swaziloo/halloween/animatronicCrow/images/AniCrow002.jpg

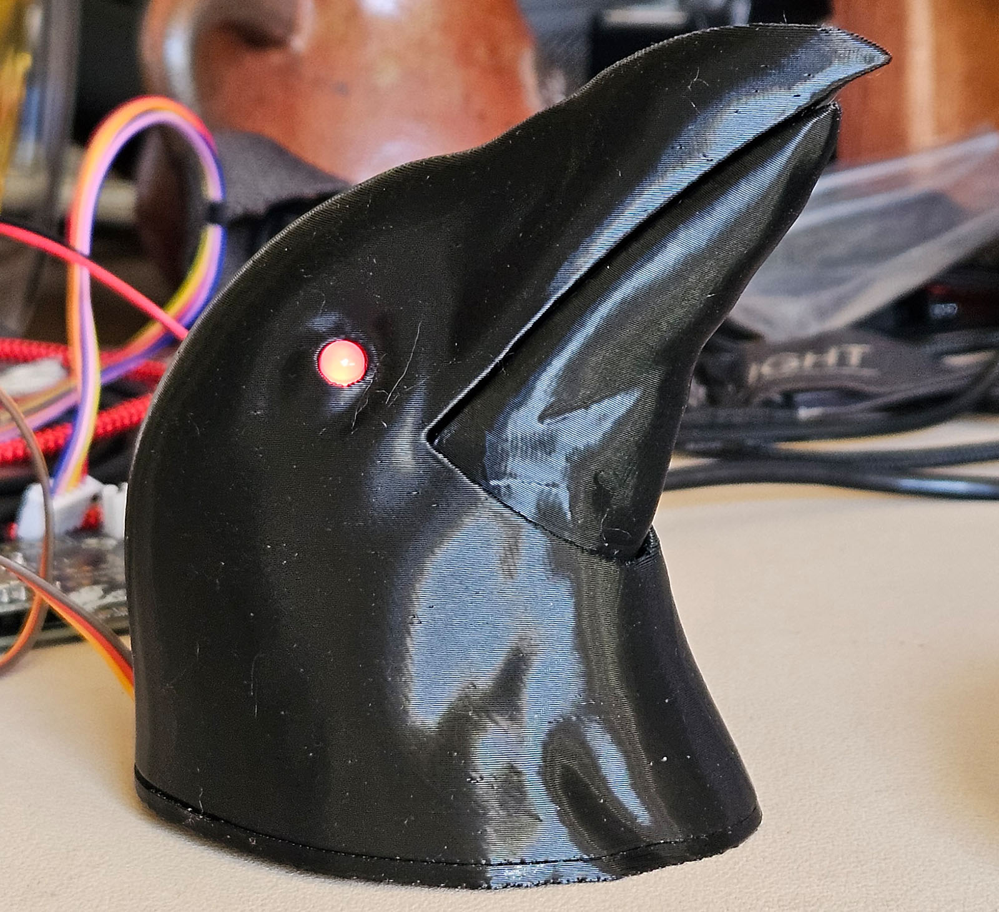
animatronicCrow/images/AniCrow002.jpg
