swaziloo/halloween/animatronicCrow/images/AniCrow003.jpg

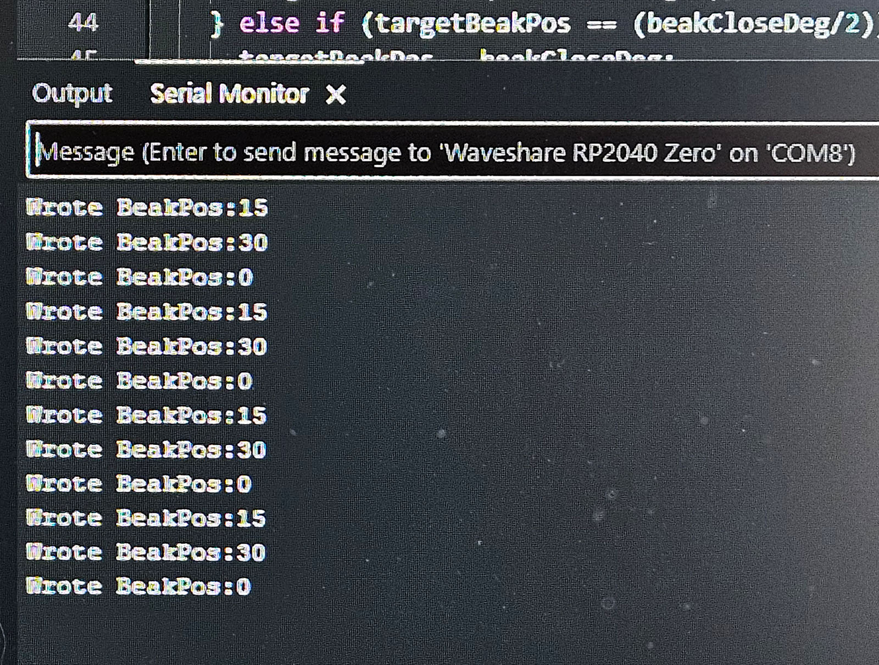
animatronicCrow/images/AniCrow003.jpg
