swaziloo/halloween/animatronicCrow/images/AniCrow004.jpg

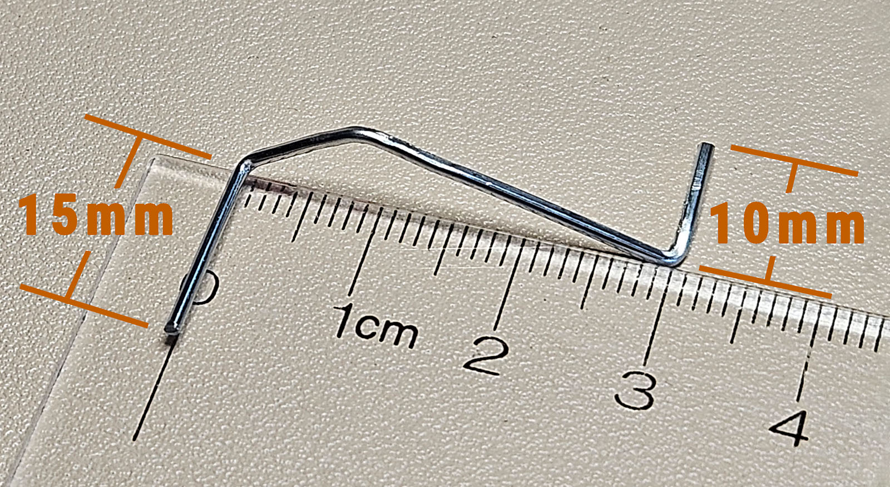
animatronicCrow/images/AniCrow004.jpg
