swaziloo/halloween/animatronicCrow/images/AniCrow005.jpg

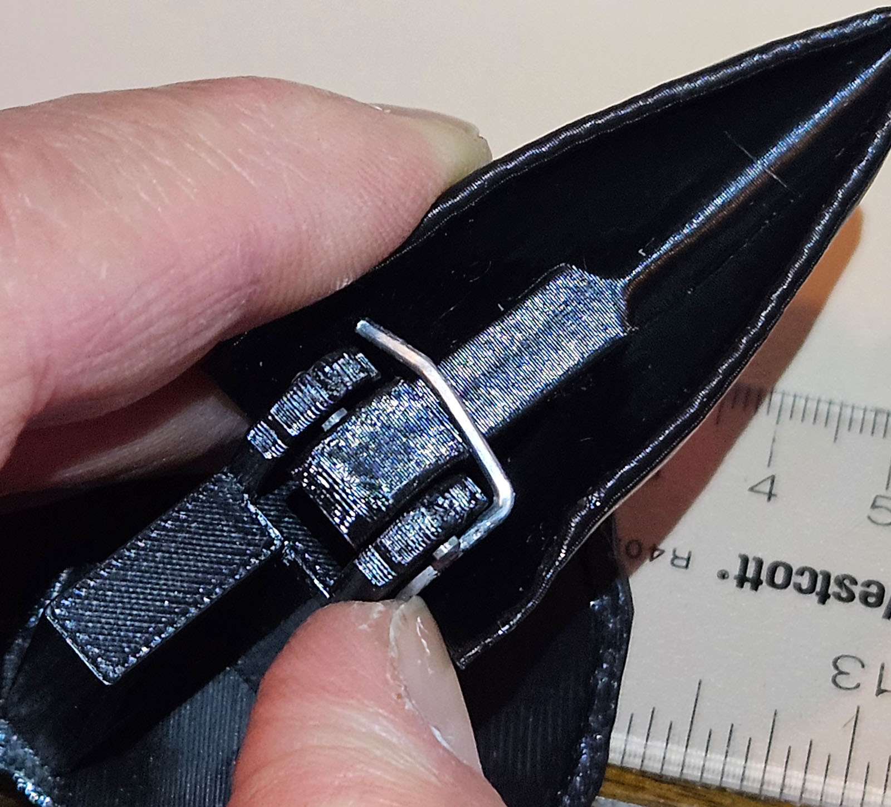
animatronicCrow/images/AniCrow005.jpg
