swaziloo/halloween/animatronicCrow/images/AniCrow006.jpg

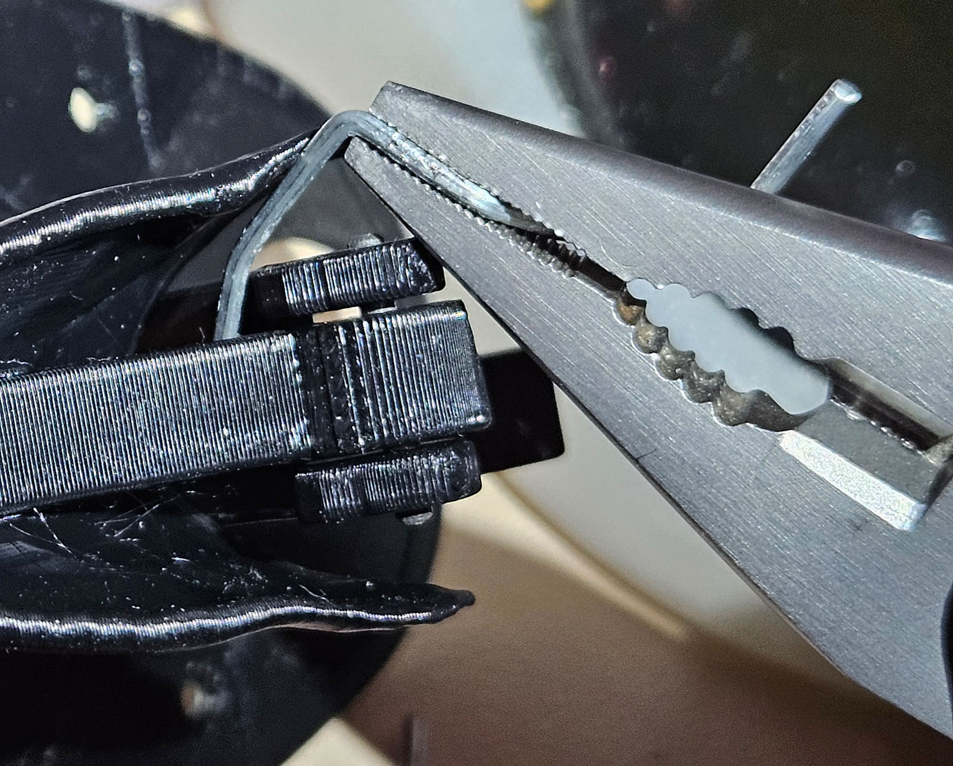
animatronicCrow/images/AniCrow006.jpg
