swaziloo/halloween/animatronicCrow/images/AniCrow007.jpg

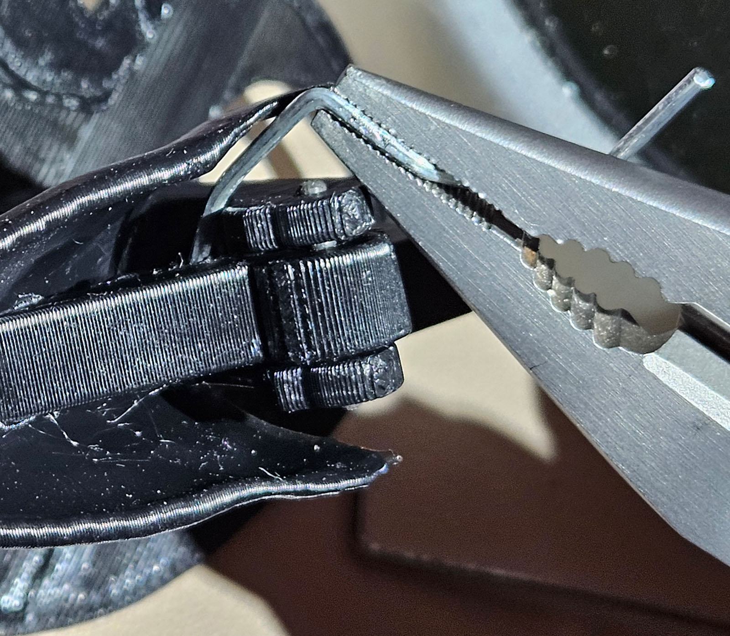
animatronicCrow/images/AniCrow007.jpg
