swaziloo/halloween/animatronicCrow/images/AniCrow008.jpg

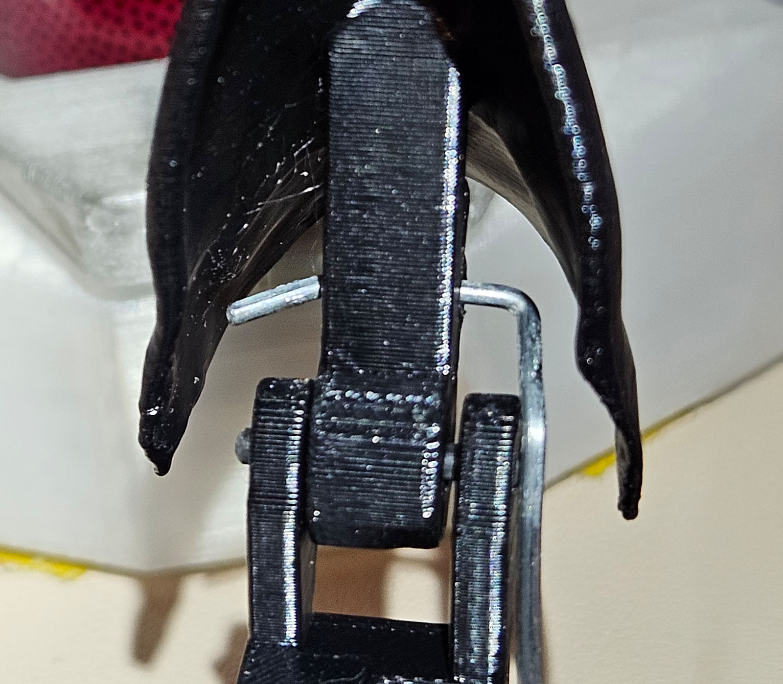
animatronicCrow/images/AniCrow008.jpg
