swaziloo/halloween/animatronicCrow/images/AniCrow009.jpg

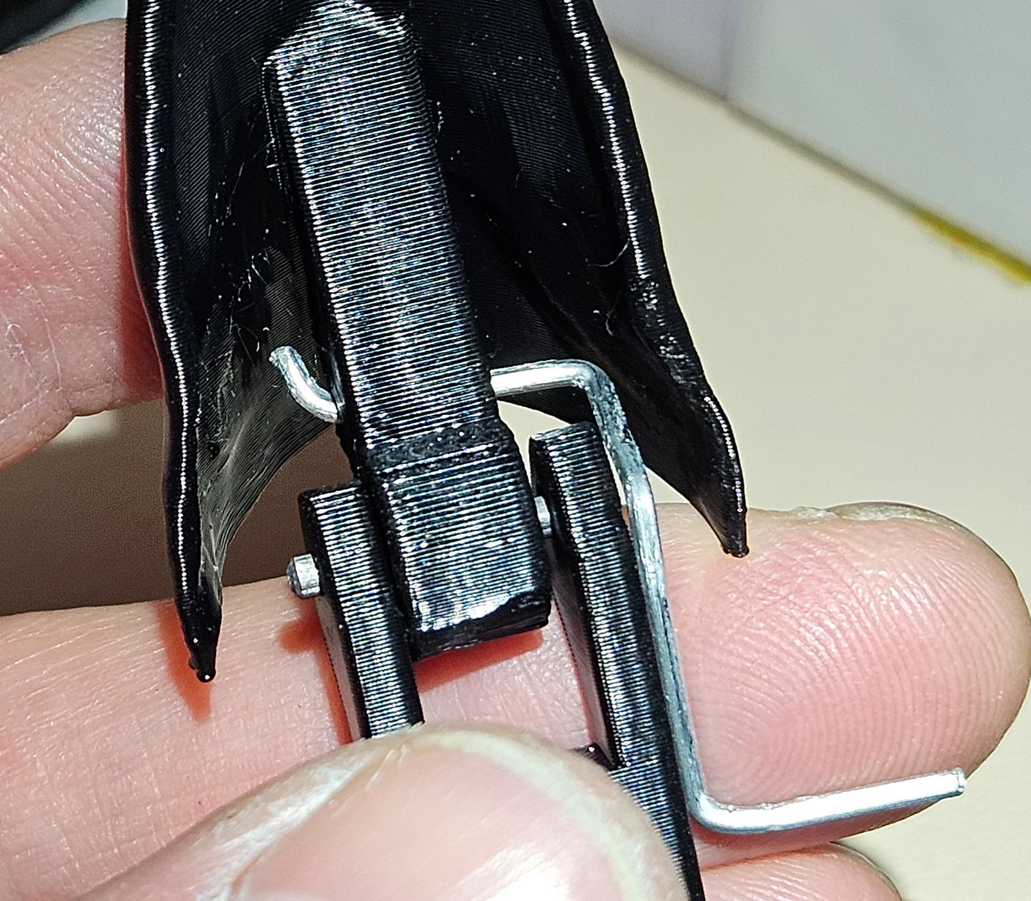
animatronicCrow/images/AniCrow009.jpg
