swaziloo/halloween/animatronicCrow/images/AniCrow019.jpg

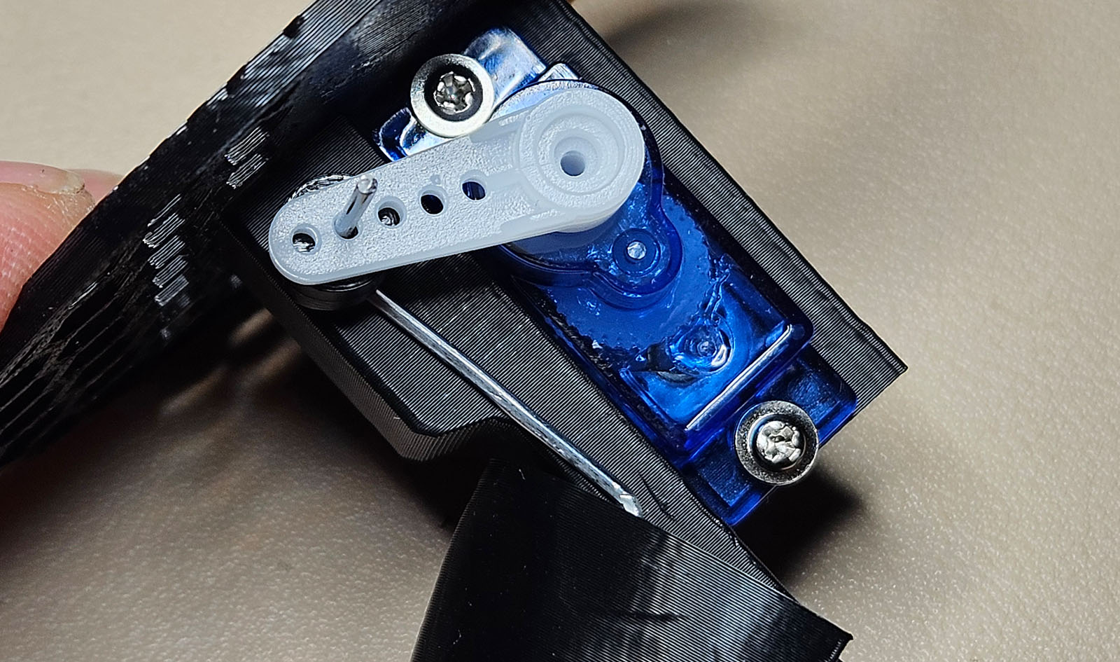
animatronicCrow/images/AniCrow019.jpg
