swaziloo/halloween/animatronicCrow/images/AniCrow020.png

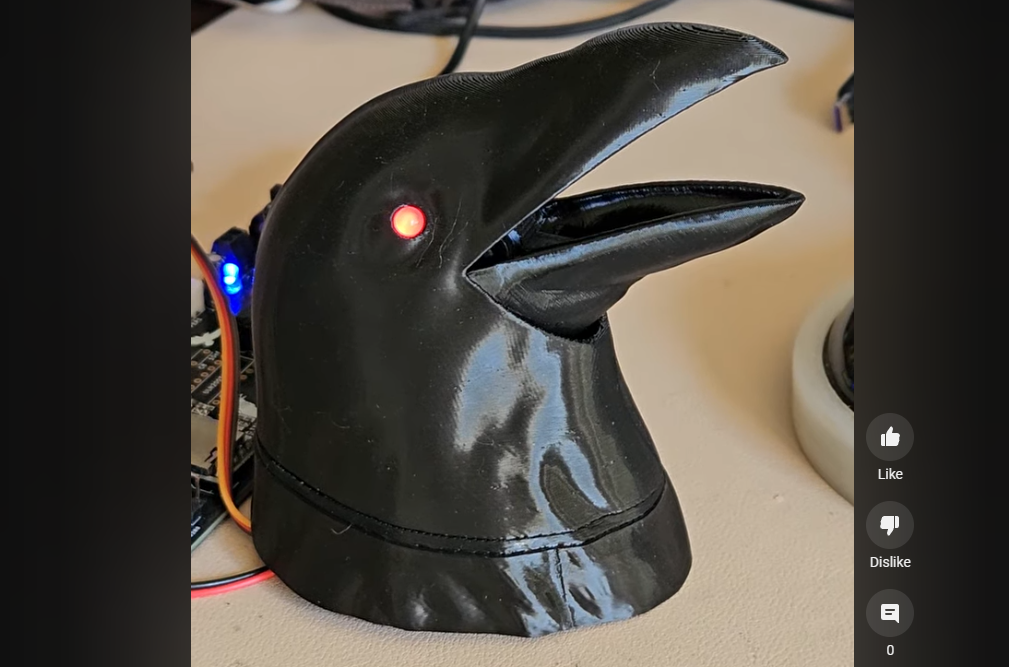
animatronicCrow/images/AniCrow020.png
