swaziloo/halloween/animatronicCrow/images/AniCrow021.png

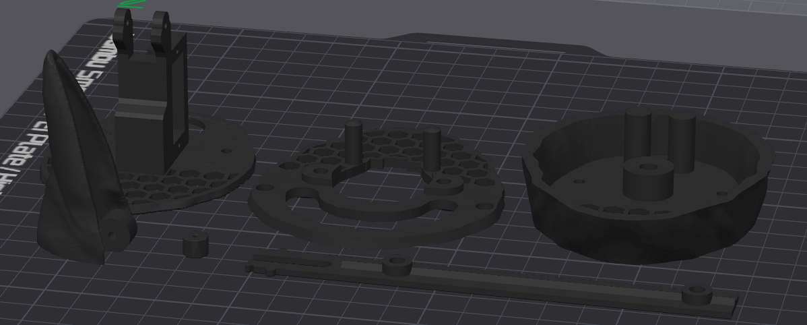
animatronicCrow/images/AniCrow021.png
