swaziloo/halloween/animatronicCrow/images/AniCrow023.jpg

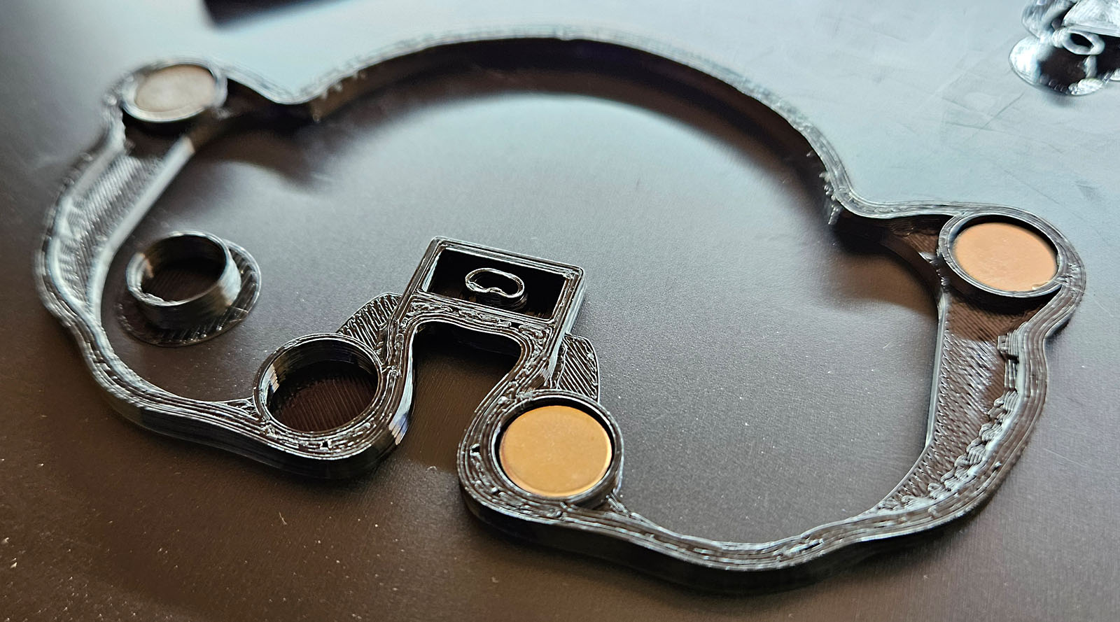
animatronicCrow/images/AniCrow023.jpg
