swaziloo/halloween/animatronicCrow/images/AniCrow025.jpg

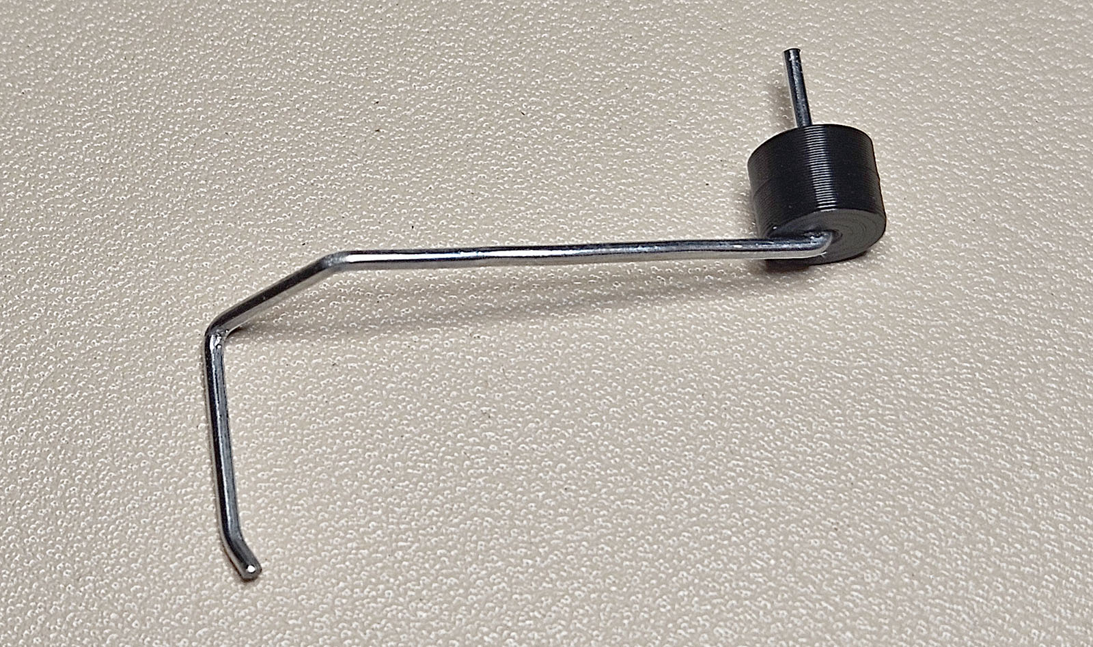
animatronicCrow/images/AniCrow025.jpg
