swaziloo/halloween/animatronicCrow/images/AniCrow026.png

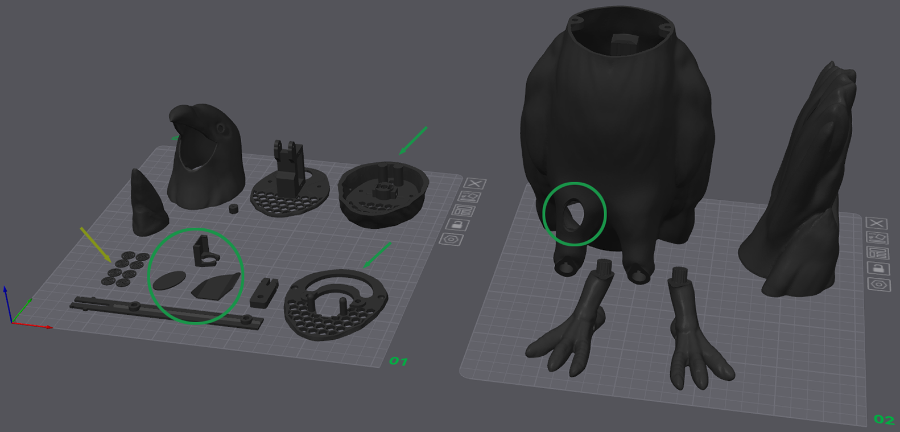
animatronicCrow/images/AniCrow026.png
