swaziloo/halloween/animatronicCrow/images/AniCrow027.png

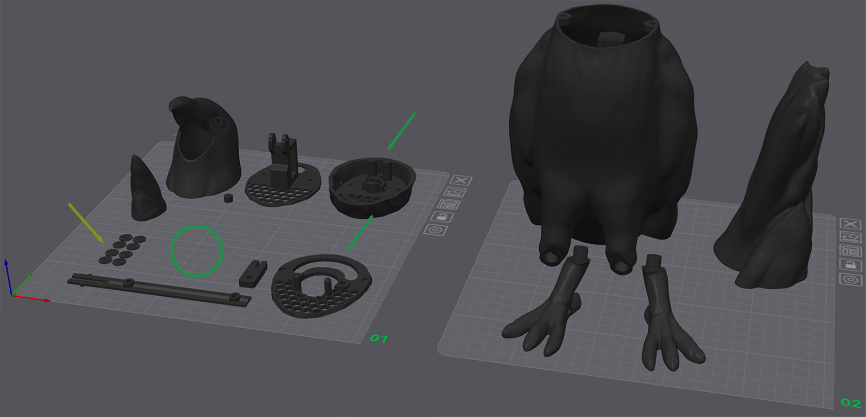
animatronicCrow/images/AniCrow027.png
