swaziloo/halloween/animatronicCrow/images/AniCrow028.jpg

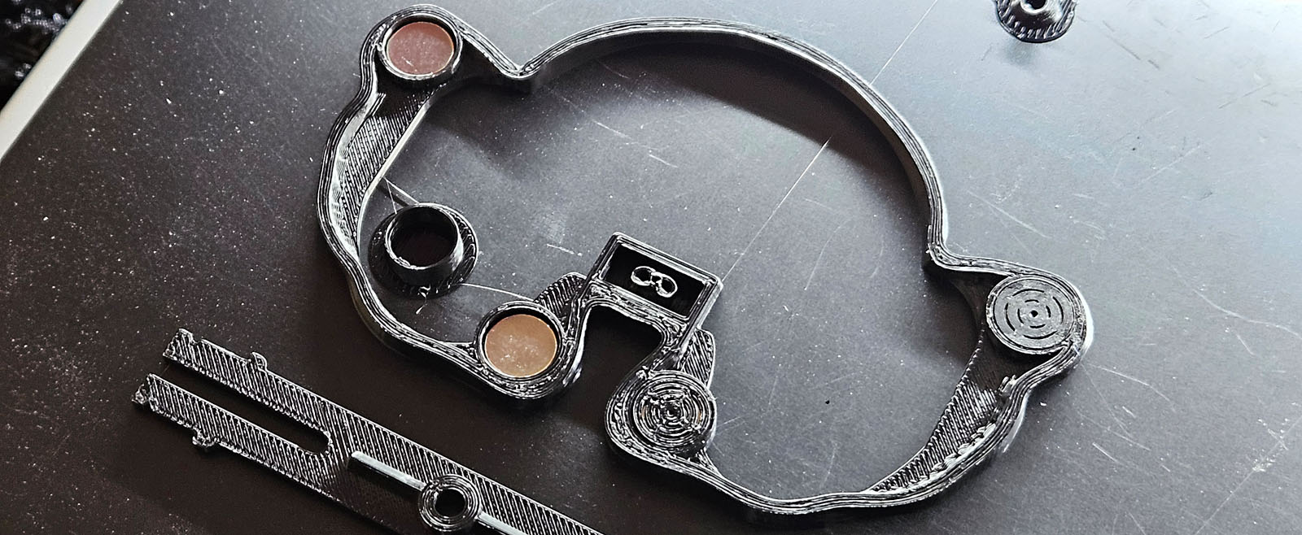
animatronicCrow/images/AniCrow028.jpg
