swaziloo/halloween/animatronicCrow/images/AniCrow035.jpg

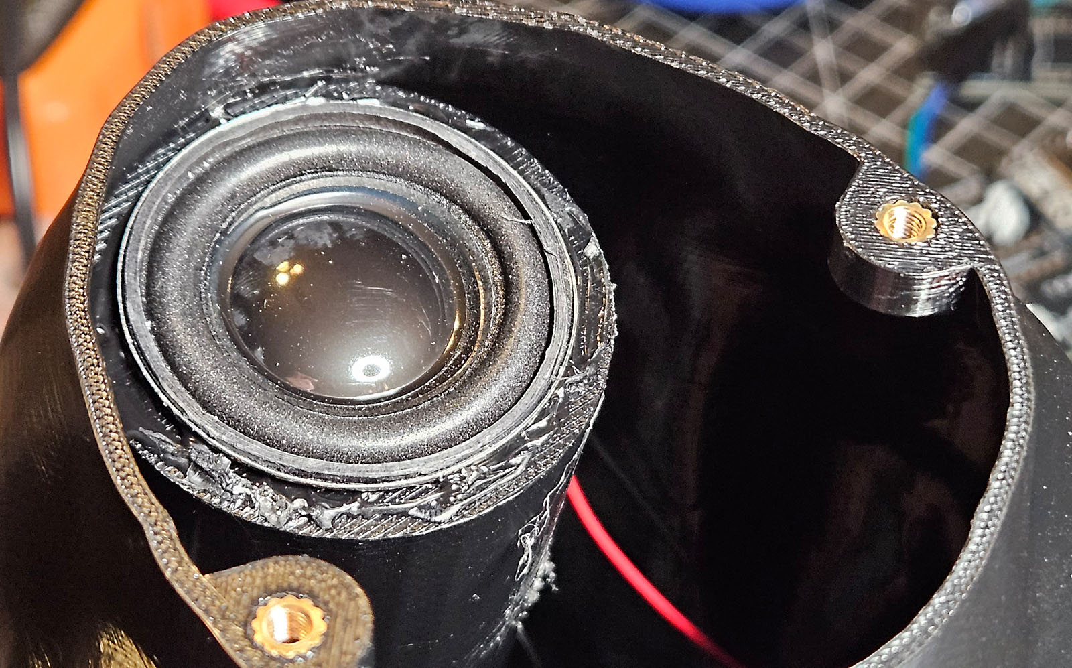
animatronicCrow/images/AniCrow035.jpg
