swaziloo/halloween/animatronicCrow/images/AniCrow037.jpg

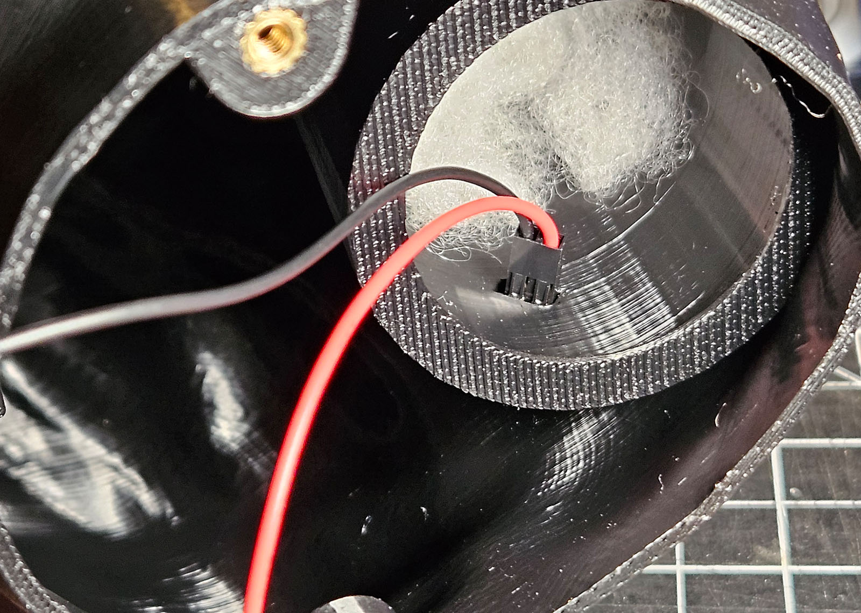
animatronicCrow/images/AniCrow037.jpg
