swaziloo/halloween/animatronicCrow/images/AniCrow041.jpg

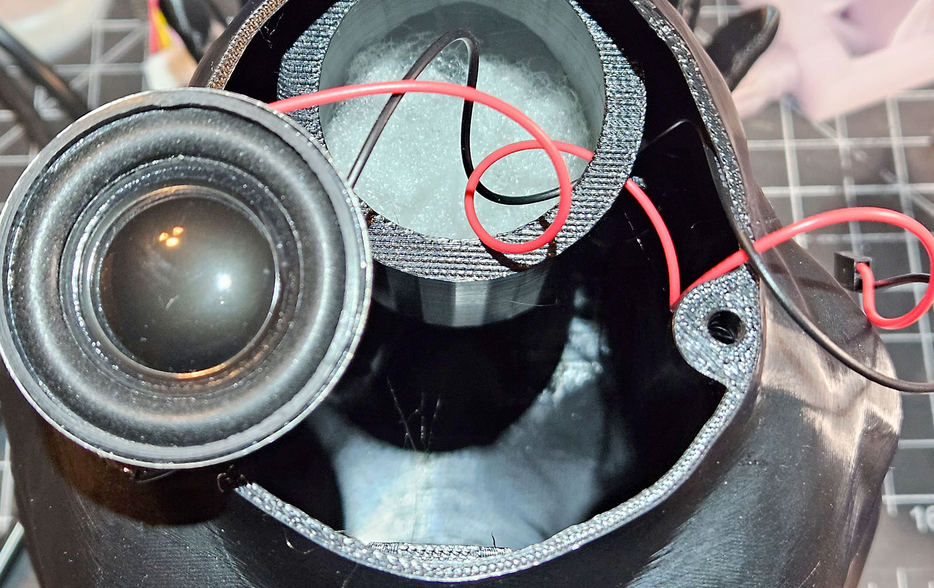
animatronicCrow/images/AniCrow041.jpg
