swaziloo/halloween/animatronicCrow/images/AniCrow042.jpg

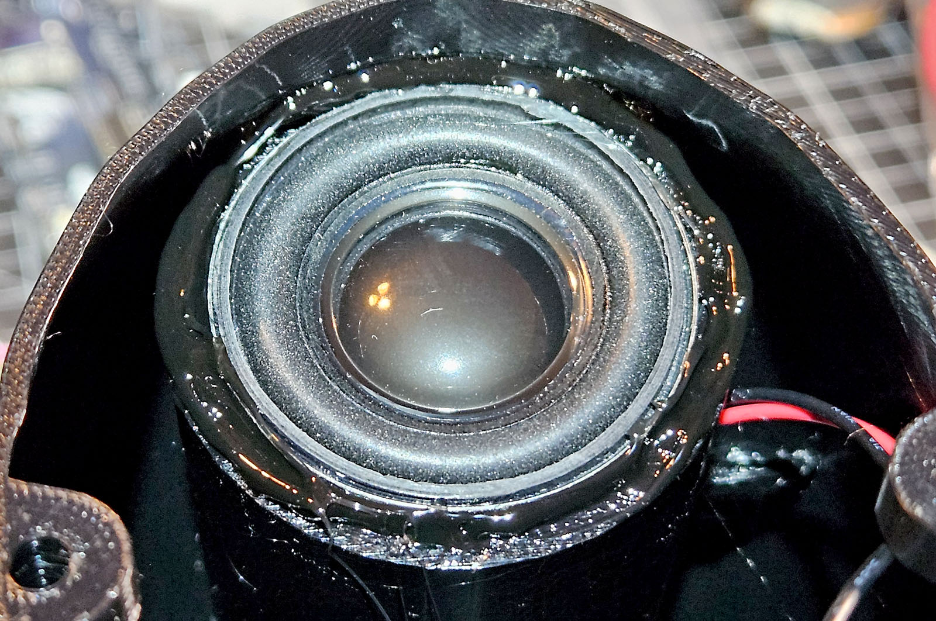
animatronicCrow/images/AniCrow042.jpg
