swaziloo/halloween/animatronicCrow/images/AniCrow043.jpg

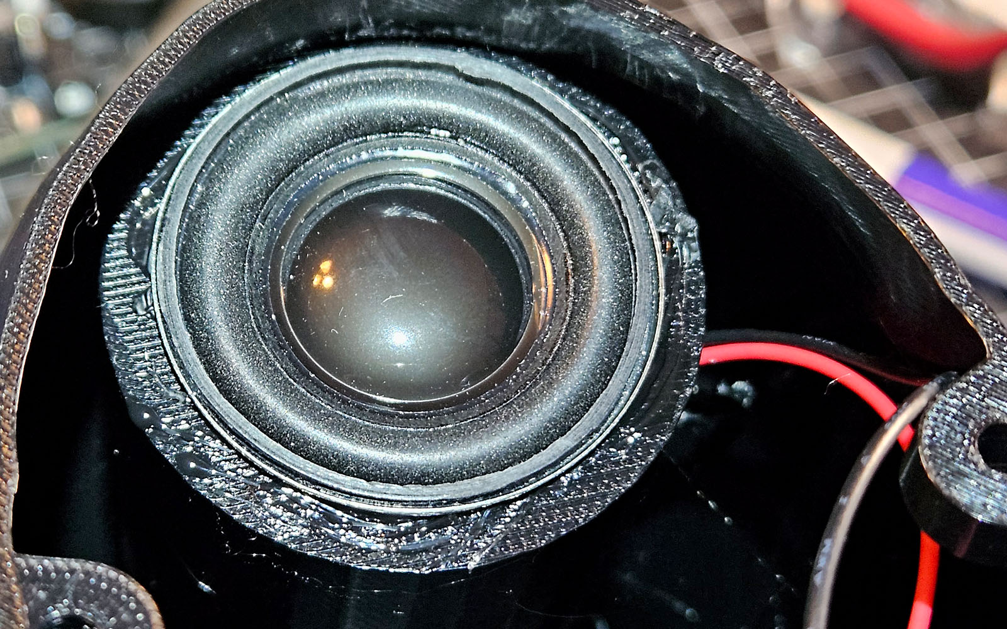
animatronicCrow/images/AniCrow043.jpg
