swaziloo/halloween/animatronicCrow/images/AniCrow044.jpg

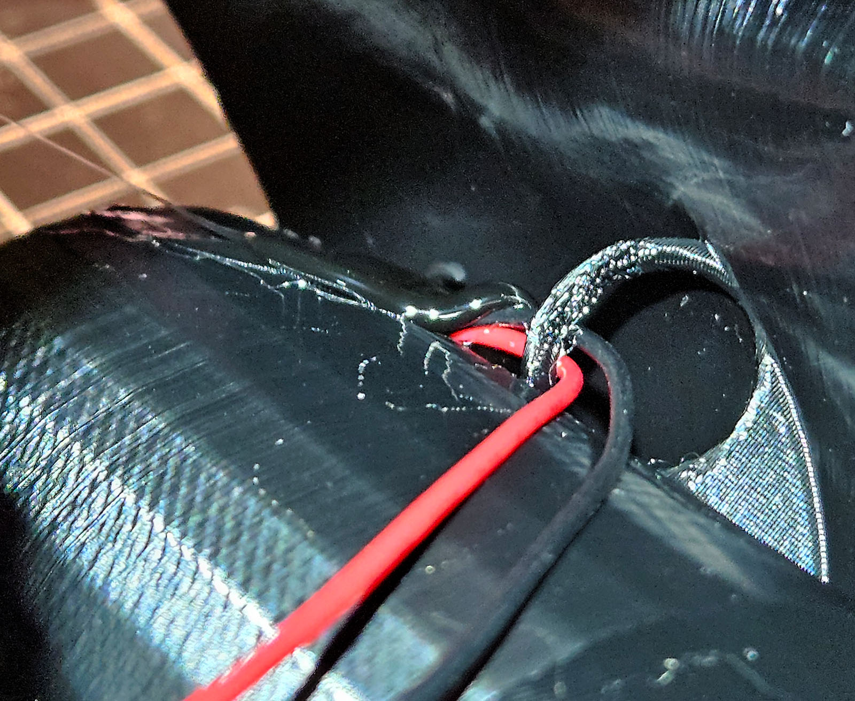
animatronicCrow/images/AniCrow044.jpg
