swaziloo/halloween/animatronicCrow/images/AniCrow047.jpg

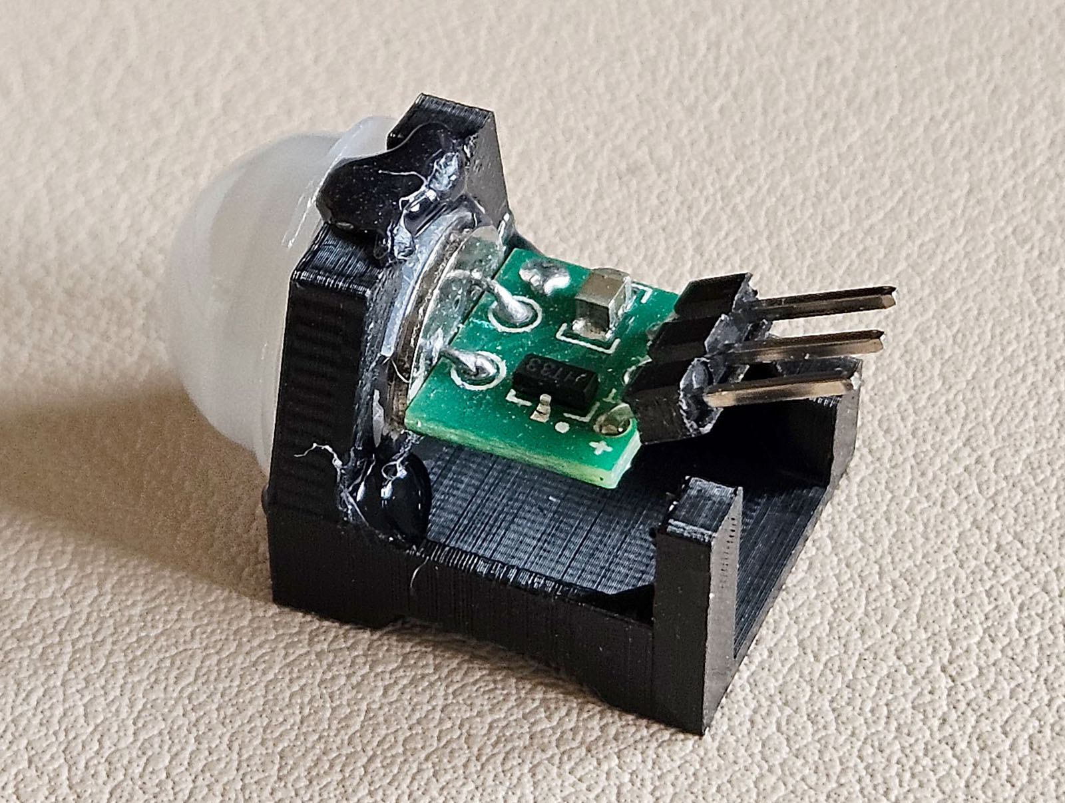
animatronicCrow/images/AniCrow047.jpg
