swaziloo/halloween/animatronicCrow/images/AniCrow050.jpg

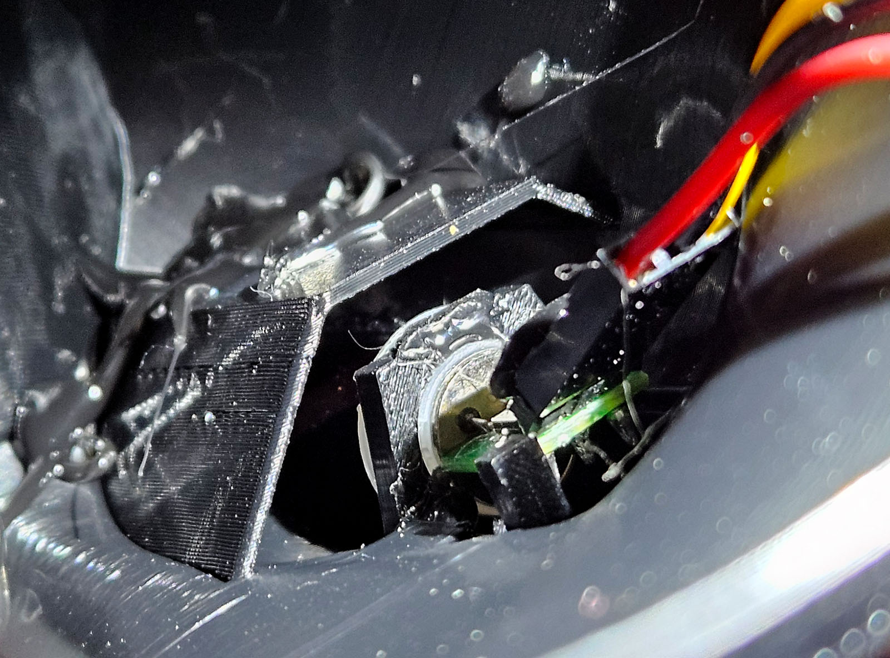
animatronicCrow/images/AniCrow050.jpg
