swaziloo/halloween/creatureControl/images/cc5x12-001.png

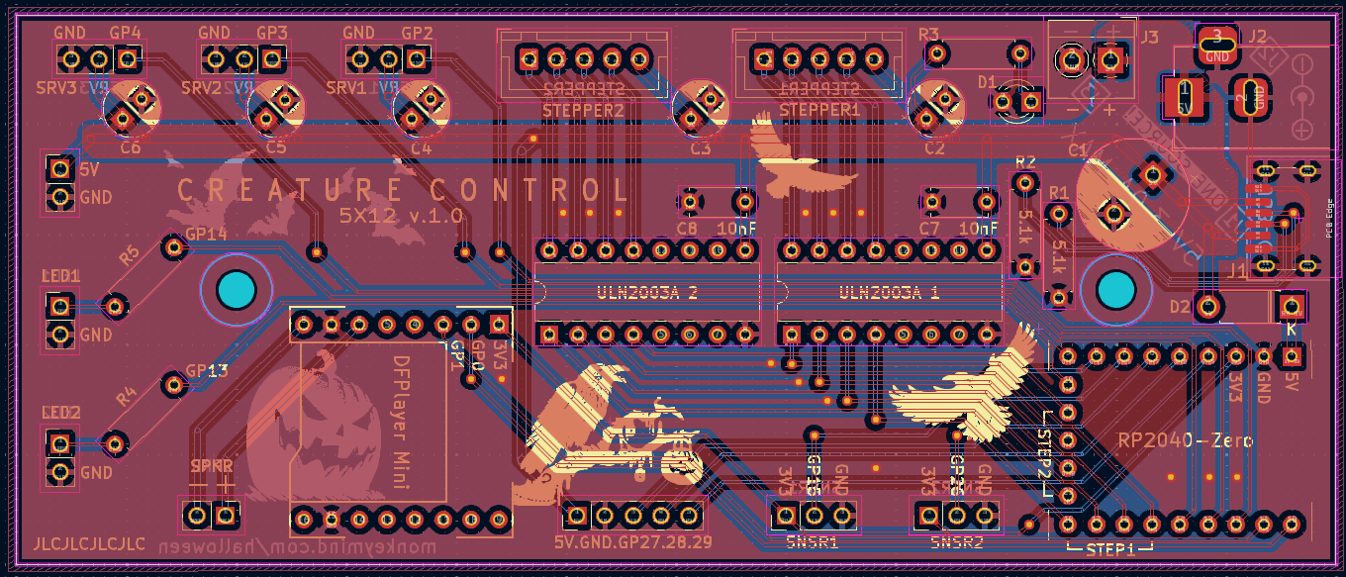
creatureControl/images/cc5x12-001.png
