swaziloo/halloween/creatureControl/images/cc5x12-003.png

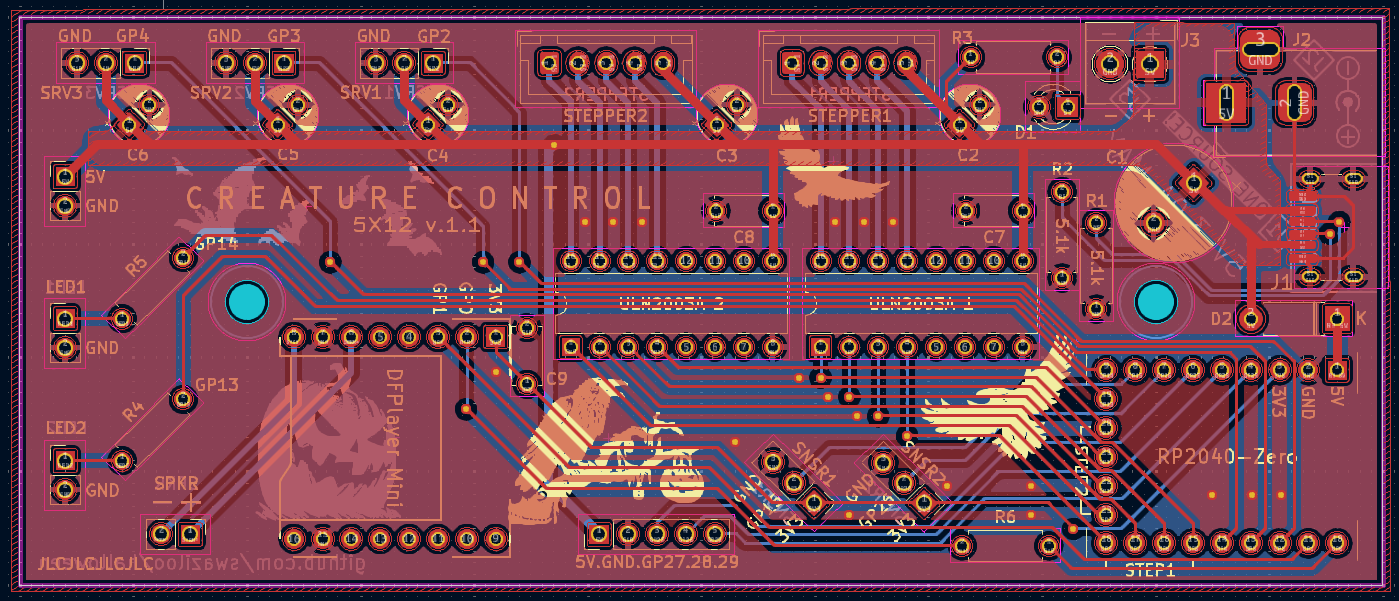
creatureControl/images/cc5x12-003.png
