swaziloo/halloween/animatronicCrow/stl/HeadServoBeakMountPlate.stl

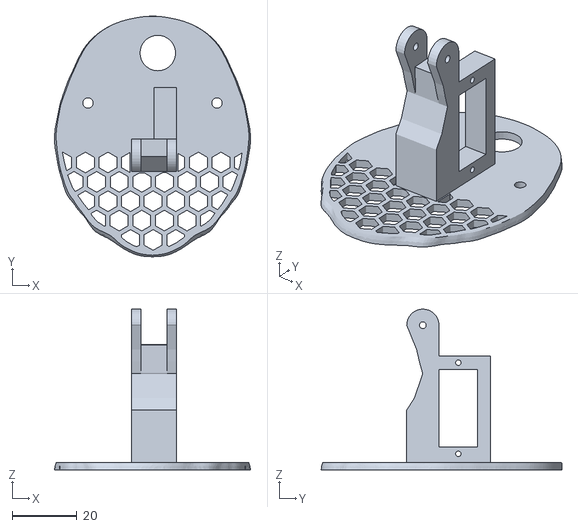
[picture p69: CAD file, 2025-10-06]
animatronicCrow/stl/HeadServoBeakMountPlate.stl
60.7 x 74.6 x 49.8
