swaziloo/halloween/animatronicCrow/stl/HeadStepperCollar.stl

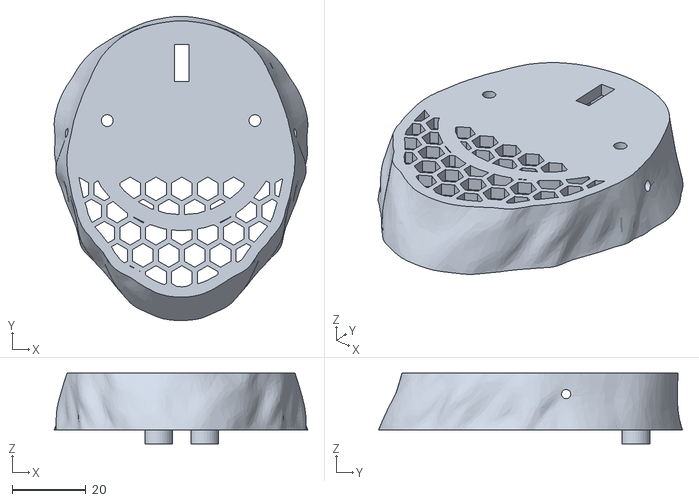
[picture p70: CAD file, 2025-09-22]
animatronicCrow/stl/HeadStepperCollar.stl
68.7 x 82.3 x 19.2
